HekiNav/helsinki-live-train-map/PCB/Helsinki-LED-Train-Map.jpg

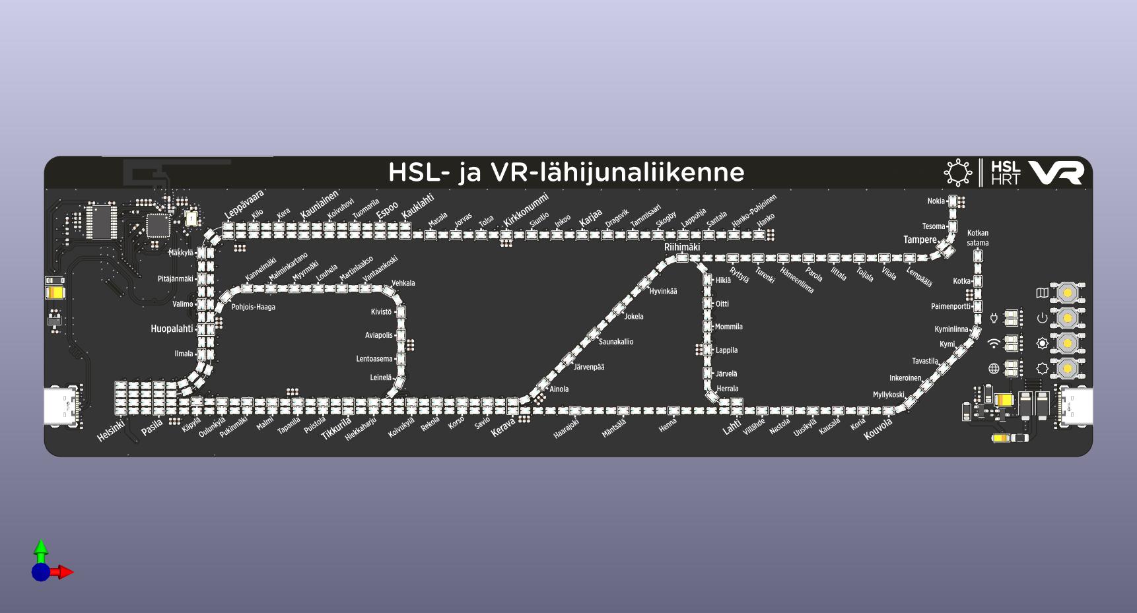
PCB/Helsinki-LED-Train-Map.jpg
